angular-mk/angularmk-rgb/PCB_Antenna_Lib/JPGs/SWRA416.jpg

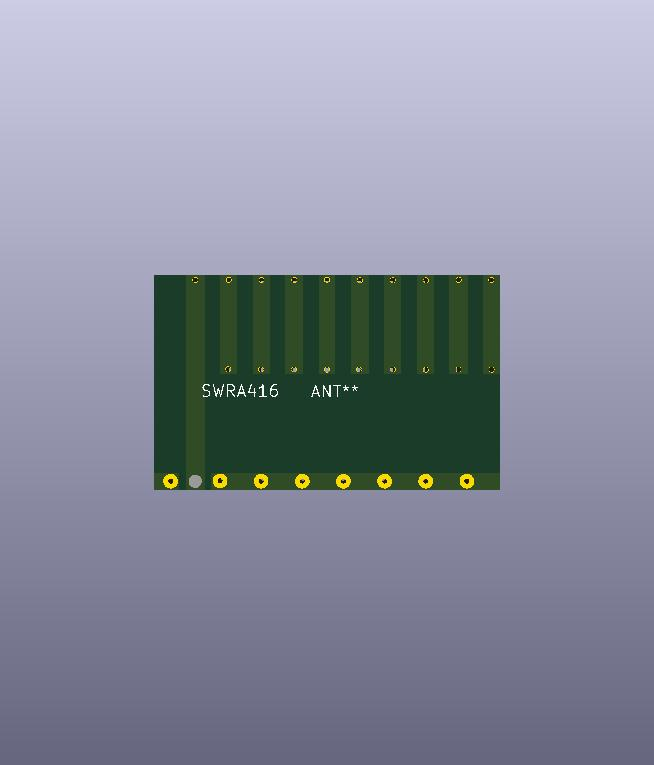
PCB_Antenna_Lib/JPGs/SWRA416.jpg
