angular-mk/angularmk-rgb/MX_Alps_Hybrid.pretty-master/Screenshots/Render-Bottomside.png

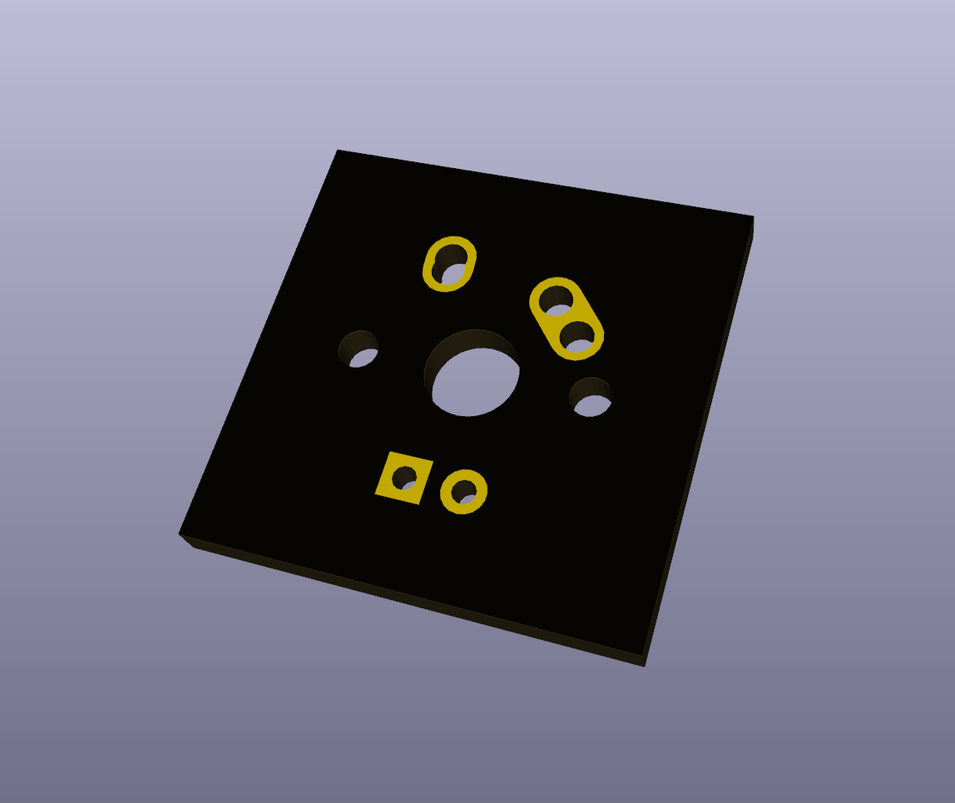
MX_Alps_Hybrid.pretty-master/Screenshots/Render-Bottomside.png
