angular-mk/angularmk-rgb/MX_Alps_Hybrid.pretty-master/Screenshots/Render-Topside.png

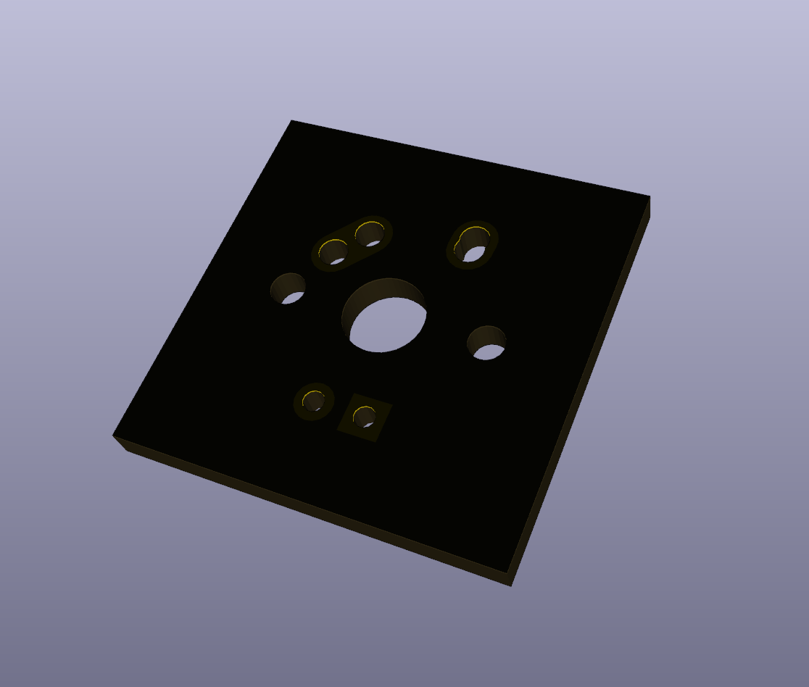
MX_Alps_Hybrid.pretty-master/Screenshots/Render-Topside.png
