angular-mk/angularmk-rgb/MX_Alps_Hybrid.pretty-master/Screenshots/Schematic.png

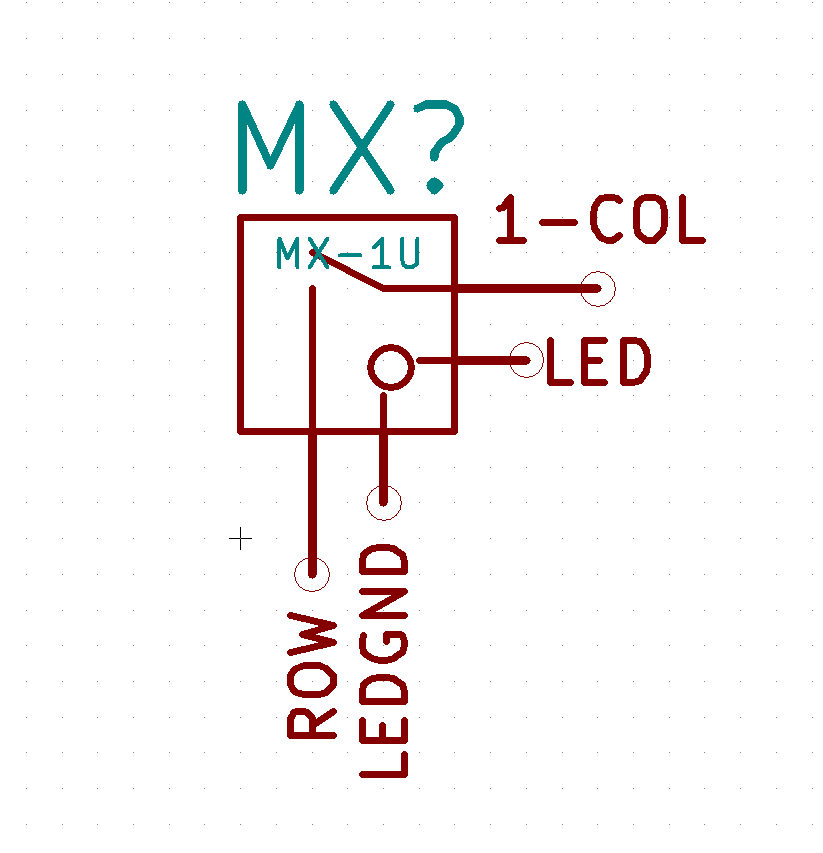
MX_Alps_Hybrid.pretty-master/Screenshots/Schematic.png
