angular-mk/angularmk-rgb/PCB_Antenna_Lib/Datasheets/AN91445A.png

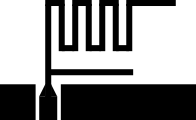
PCB_Antenna_Lib/Datasheets/AN91445A.png
