angular-mk/angularmk-rgb/PCB_Antenna_Lib/Datasheets/SWRA118.png

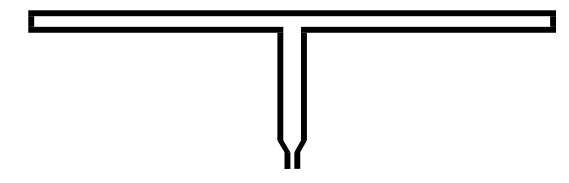
PCB_Antenna_Lib/Datasheets/SWRA118.png
