angular-mk/angularmk-rgb/PCB_Antenna_Lib/Datasheets/SWRA350A.png

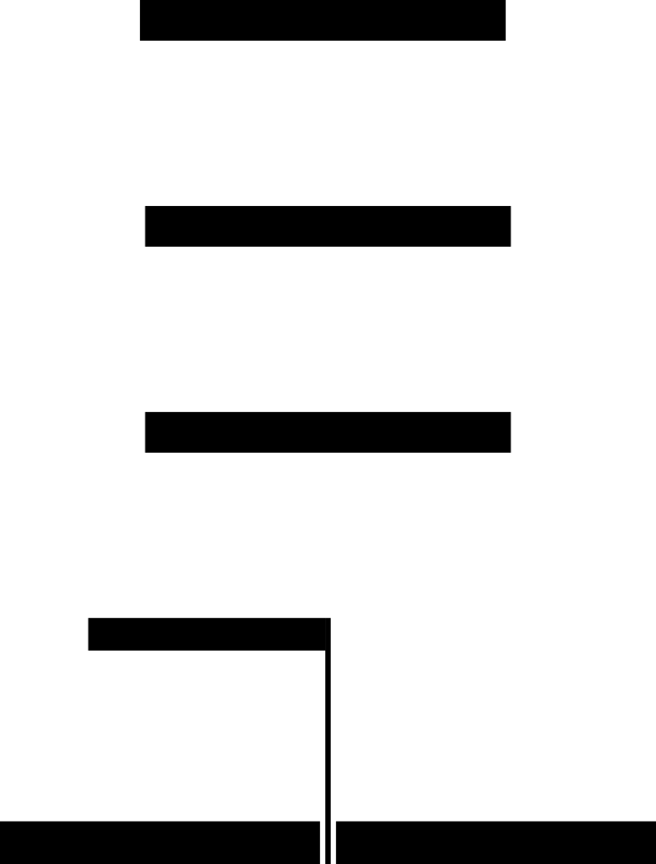
PCB_Antenna_Lib/Datasheets/SWRA350A.png
