angular-mk/angularmk-rgb/PCB_Antenna_Lib/Datasheets/SWRA350B.png

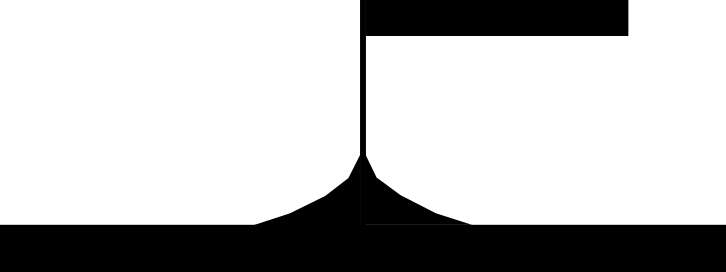
PCB_Antenna_Lib/Datasheets/SWRA350B.png
