angular-mk/angularmk-rgb/PCB_Antenna_Lib/Datasheets/swra416A.png

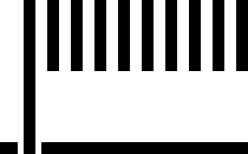
PCB_Antenna_Lib/Datasheets/swra416A.png
