angular-mk/angularmk-rgb/PCB_Antenna_Lib/JPGs/AN91445.jpg

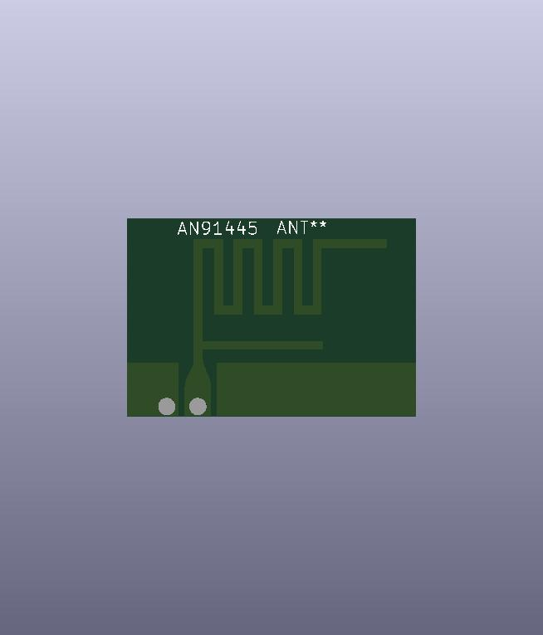
PCB_Antenna_Lib/JPGs/AN91445.jpg
