angular-mk/angularmk-rgb/PCB_Antenna_Lib/JPGs/SWRA117D.jpg

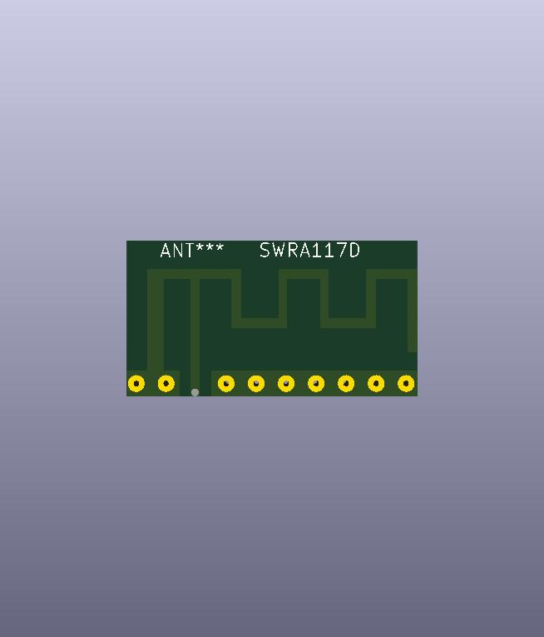
PCB_Antenna_Lib/JPGs/SWRA117D.jpg
