angular-mk/angularmk-rgb/Case Design/Test Render.png

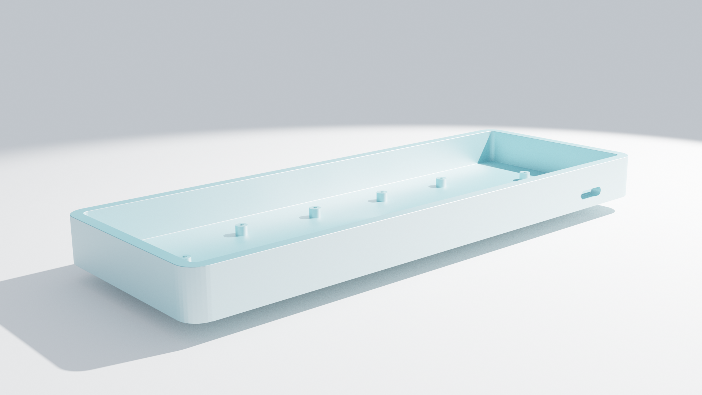
Case Design/Test Render.png
